mbvs/growlight/src/defines.h

#ifndef _DEFINES_
#define _DEFINES_

#define LED_TIME 4
#define LED_ON 3
#define LED_OFF 2

#define BUTTON_MODE 7
#define BUTTON_UP 6
#define BUTTON_DOWN 5
#define BUTTON_CONFIRM A1

#define SWITCH_TIMER 11
#define SWITCH_LIGHT 12

#define FET 10

#define CLK 9 // display clock
#define DIO 8 // display data

#endif
